weesing/doorlock/models/stls/SG90ServoBracket.stl

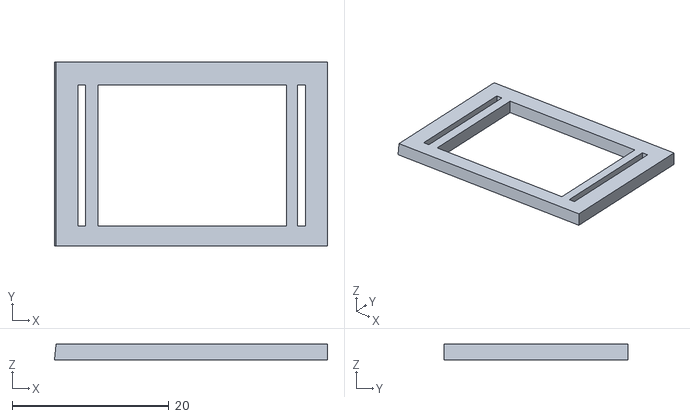
[picture p18: CAD file, 2019-09-11, last stored version]
models/stls/SG90ServoBracket.stl
34.8 x 23.4 x 2.00
