weesing/doorlock/models/ControllerHousing.3mf

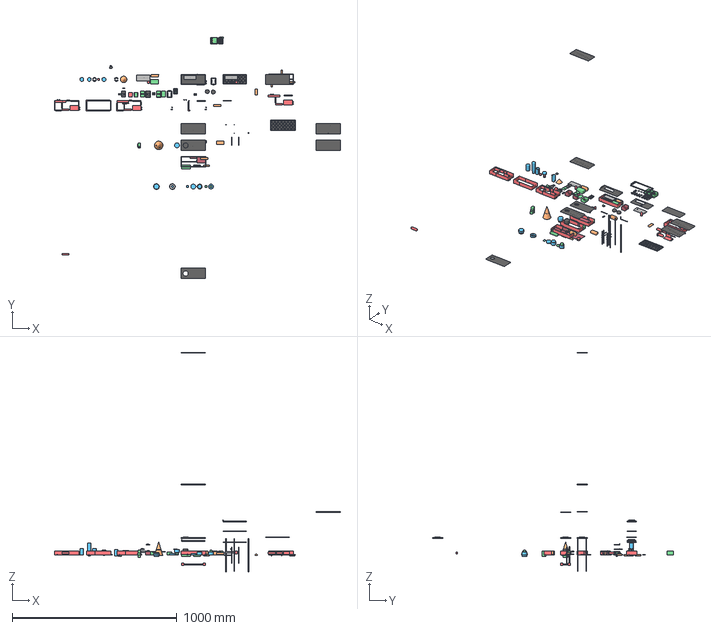
[picture p19: CAD file, 2019-09-11, last stored version]
models/ControllerHousing.3mf
1735.2 x 1465.2 x 1330.1 mm
