weesing/doorlock/models/gears/Linear_Servo_HiTEC_HS-645MG_/files/LINEAR_SERVO_017_8p4mmGearThickness_1p47.stl

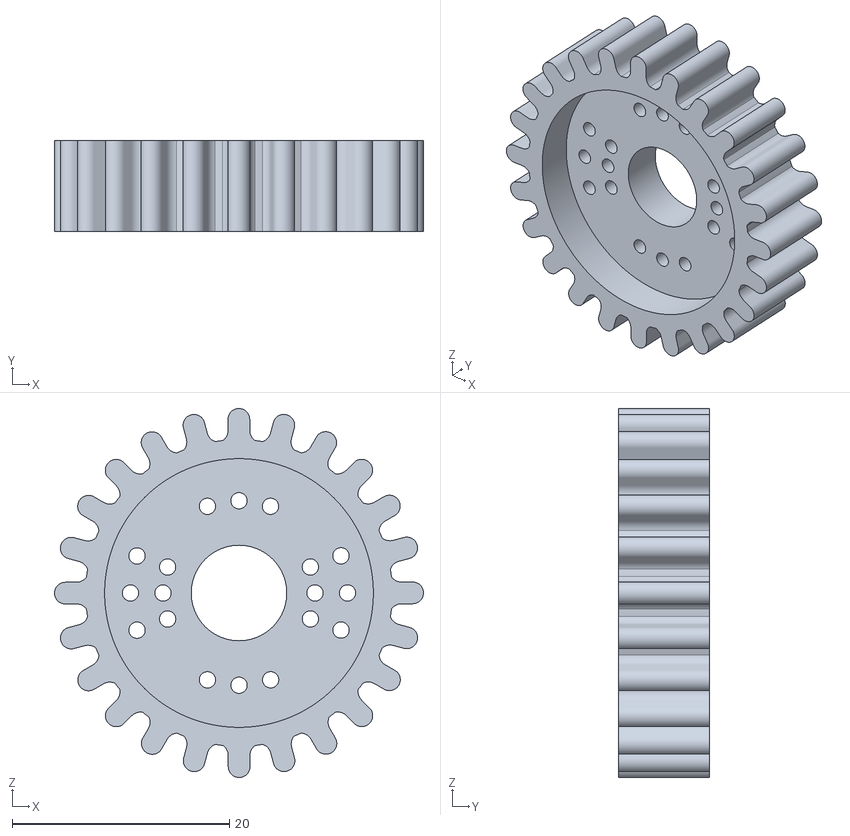
[picture p20: CAD file, 2019-09-11, last stored version]
models/gears/Linear_Servo_HiTEC_HS-645MG_/files/LINEAR_SERVO_017_8p4mmGearThickness_1p47.stl
34.0 x 8.40 x 34.0
