weesing/doorlock/models/gears/parametric_involute_gear_v5.0_2.3mf

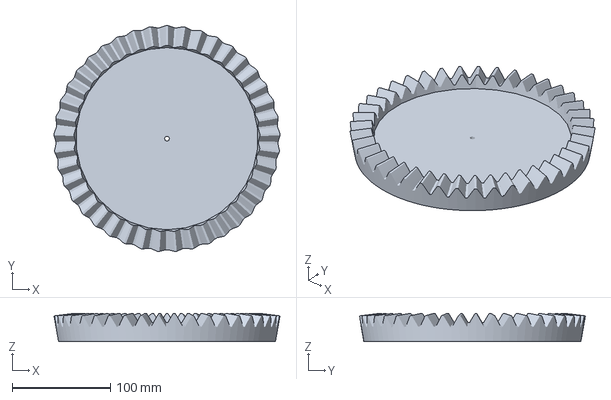
[picture p21: CAD file, 2019-09-11, last stored version]
models/gears/parametric_involute_gear_v5.0_2.3mf
229.7 x 229.6 x 28.7 mm
