weesing/doorlock/models/stls/ServoHousing.stl

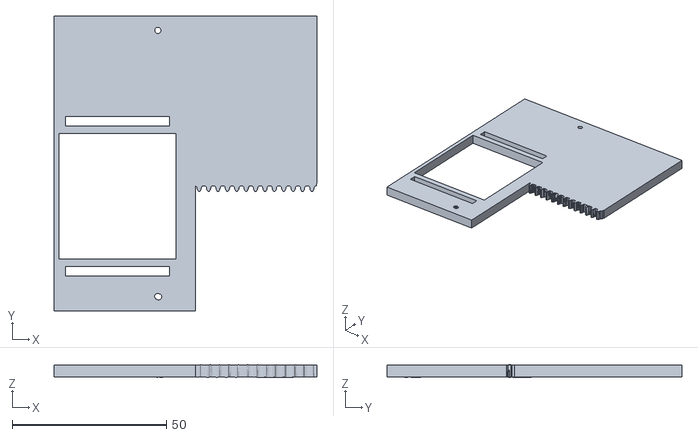
[picture p22: CAD file, 2019-09-11, last stored version]
models/stls/ServoHousing.stl
85.4 x 95.7 x 4.17
