weesing/doorlock/models/BatteryHousing.3mf

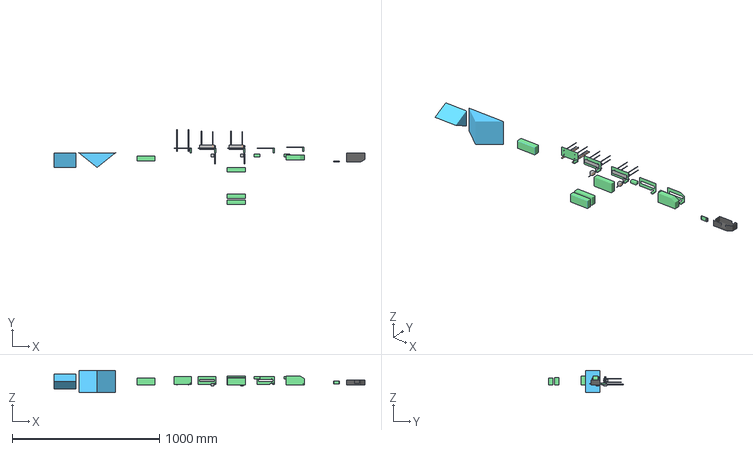
[picture p23: CAD file, 2019-09-11, last stored version]
models/BatteryHousing.3mf
2112.9 x 511.5 x 150.0 mm
