weesing/doorlock/models/stls/ArmsPlate.stl

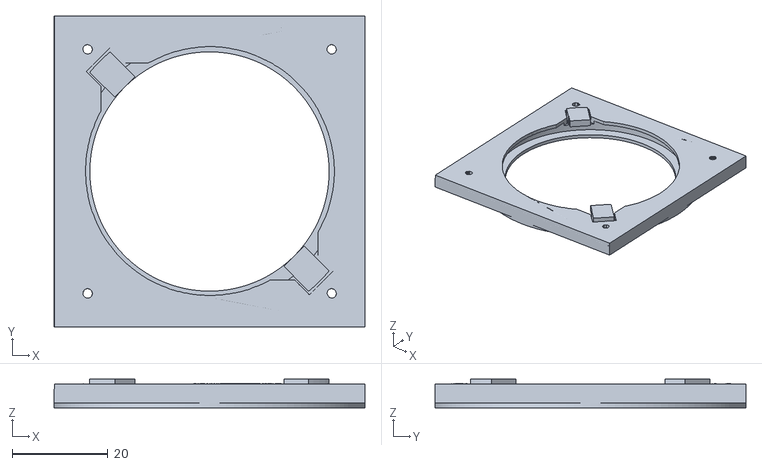
[picture p24: CAD file, 2019-09-11, last stored version]
models/stls/ArmsPlate.stl
65.0 x 65.0 x 6.00
