weesing/doorlock/models/DoorLock_Prototype_HandKnob.3mf

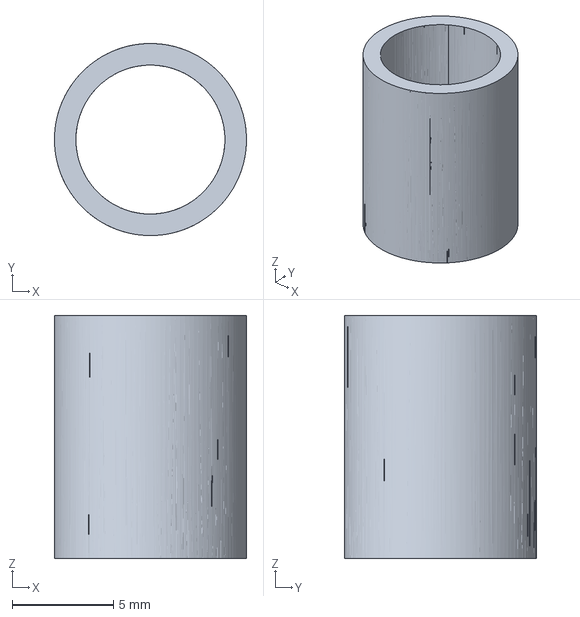
[picture p25: CAD file, 2019-09-11, last stored version]
models/DoorLock_Prototype_HandKnob.3mf
9.50 x 9.50 x 12.0 mm
