weesing/doorlock/models/RFIDHousing.3mf

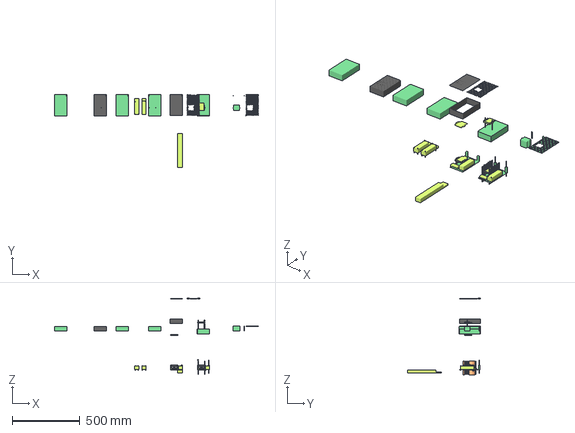
[picture p26: CAD file, 2019-09-11, last stored version]
models/RFIDHousing.3mf
1510.3 x 537.3 x 565.3 mm
