weesing/doorlock/models/DoorLock_Prototype_Plate.3mf

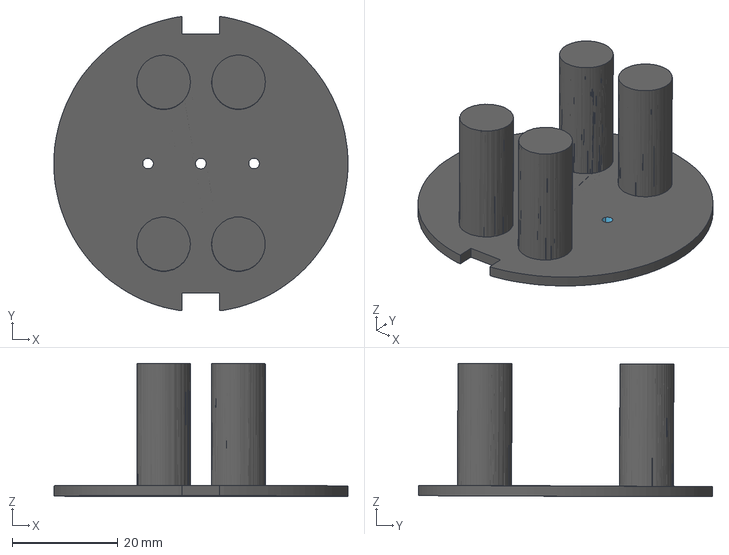
[picture p27: CAD file, 2019-09-11, last stored version]
models/DoorLock_Prototype_Plate.3mf
55.5 x 55.5 x 25.2 mm
