weesing/doorlock/models/Knob.3mf

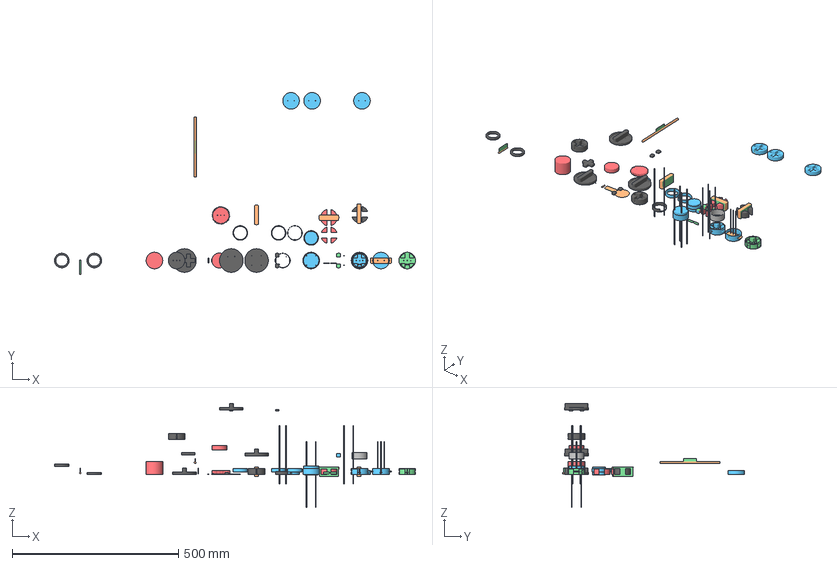
[picture p28: CAD file, 2019-09-11, last stored version]
models/Knob.3mf
1087.1 x 547.9 x 314.5 mm
