weesing/doorlock/models/Gearset.3mf

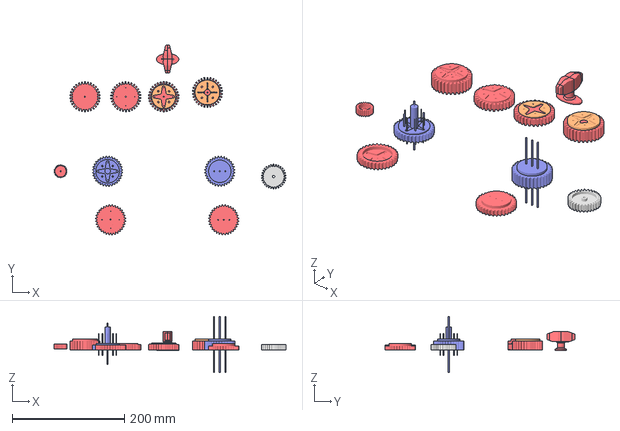
[picture p29: CAD file, 2019-09-11, last stored version]
models/Gearset.3mf
413.5 x 338.5 x 100.0 mm
