weesing/doorlock/models/ControllerHousing1.3mf

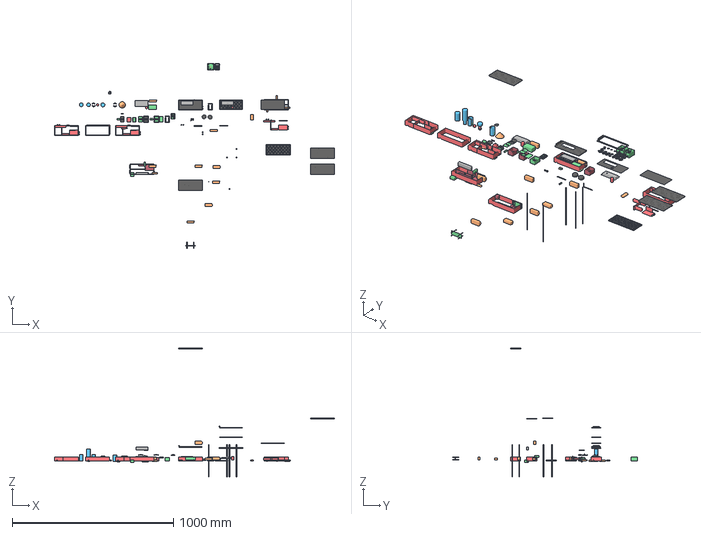
[picture p30: CAD file, 2019-09-11, last stored version]
models/ControllerHousing1.3mf
1735.2 x 1145.9 x 797.5 mm
