weesing/doorlock/models/2dofjoint.3mf

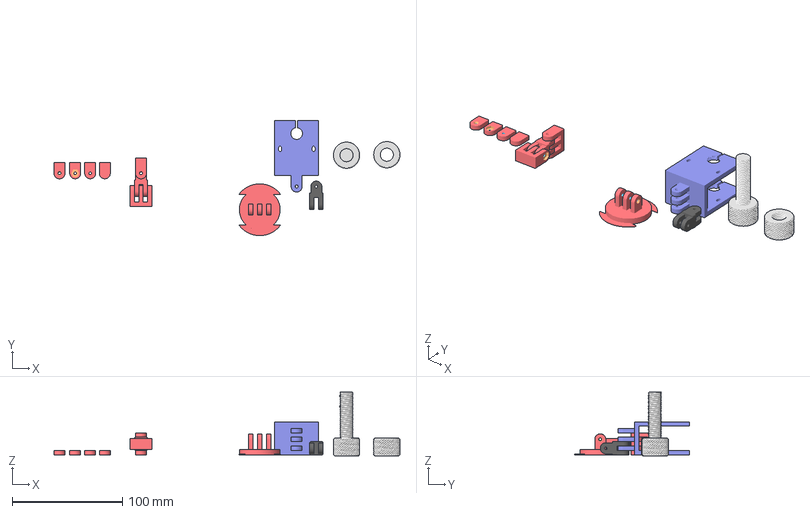
[picture p31: CAD file, 2019-09-11, last stored version]
models/2dofjoint.3mf
313.7 x 104.4 x 57.8 mm
