weesing/doorlock/models/PlateHousing.3mf

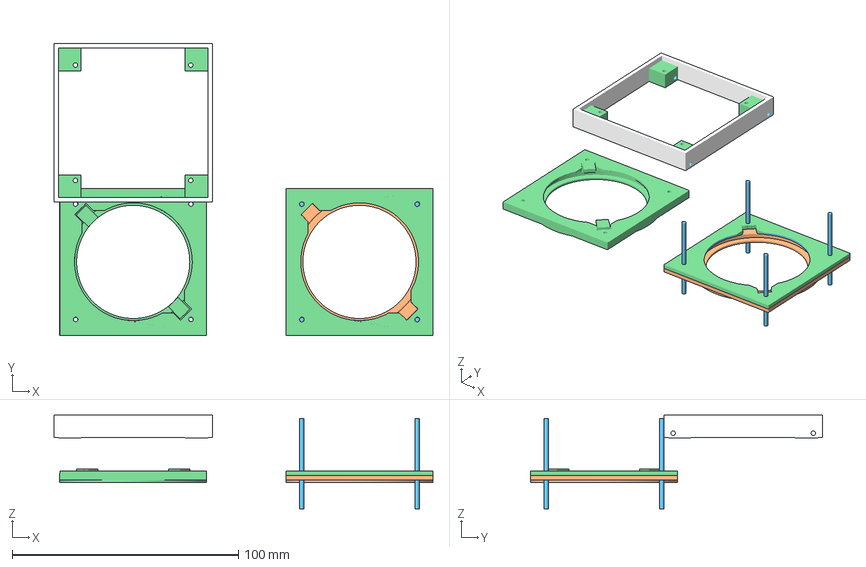
[picture p32: CAD file, 2019-09-11, last stored version]
models/PlateHousing.3mf
167.5 x 129.0 x 41.4 mm
